YaoheWangEC/daq63050-process-signal-source/software/process-signal-source-l021k8u7-4/project/src/wk_tmr.c

/* add user code begin Header */
/**
  **************************************************************************
  * @file     wk_tmr.c
  * @brief    work bench config program
  **************************************************************************
  * Copyright (c) 2025, Artery Technology, All rights reserved.
  *
  * The software Board Support Package (BSP) that is made available to
  * download from Artery official website is the copyrighted work of Artery.
  * Artery authorizes customers to use, copy, and distribute the BSP
  * software and its related documentation for the purpose of design and
  * development in conjunction with Artery microcontrollers. Use of the
  * software is governed by this copyright notice and the following disclaimer.
  *
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
  **************************************************************************
  */
/* add user code end Header */

/* Includes ------------------------------------------------------------------*/
#include "wk_tmr.h"

/* add user code begin 0 */

/* add user code end 0 */

/**
  * @brief  init tmr3 function.
  * @param  none
  * @retval none
  */
void wk_tmr3_init(void)
{
  /* add user code begin tmr3_init 0 */

  /* add user code end tmr3_init 0 */

  gpio_init_type gpio_init_struct;
  tmr_output_config_type tmr_output_struct;

  gpio_default_para_init(&gpio_init_struct);

  /* add user code begin tmr3_init 1 */

  /* add user code end tmr3_init 1 */

  /* configure the tmr3 CH1 pin */
  gpio_pin_mux_config(GPIOA, GPIO_PINS_SOURCE6, GPIO_MUX_1);
  gpio_init_struct.gpio_pins = GPIO_PINS_6;
  gpio_init_struct.gpio_mode = GPIO_MODE_MUX;
  gpio_init_struct.gpio_out_type = GPIO_OUTPUT_PUSH_PULL;
  gpio_init_struct.gpio_pull = GPIO_PULL_NONE;
  gpio_init_struct.gpio_drive_strength = GPIO_DRIVE_STRENGTH_MODERATE;
  gpio_init(GPIOA, &gpio_init_struct);

  /* configure the tmr3 CH2 pin */
  gpio_pin_mux_config(GPIOA, GPIO_PINS_SOURCE7, GPIO_MUX_1);
  gpio_init_struct.gpio_pins = GPIO_PINS_7;
  gpio_init_struct.gpio_mode = GPIO_MODE_MUX;
  gpio_init_struct.gpio_out_type = GPIO_OUTPUT_PUSH_PULL;
  gpio_init_struct.gpio_pull = GPIO_PULL_NONE;
  gpio_init_struct.gpio_drive_strength = GPIO_DRIVE_STRENGTH_MODERATE;
  gpio_init(GPIOA, &gpio_init_struct);

  /* configure the tmr3 CH3 pin */
  gpio_pin_mux_config(GPIOB, GPIO_PINS_SOURCE0, GPIO_MUX_1);
  gpio_init_struct.gpio_pins = GPIO_PINS_0;
  gpio_init_struct.gpio_mode = GPIO_MODE_MUX;
  gpio_init_struct.gpio_out_type = GPIO_OUTPUT_PUSH_PULL;
  gpio_init_struct.gpio_pull = GPIO_PULL_NONE;
  gpio_init_struct.gpio_drive_strength = GPIO_DRIVE_STRENGTH_MODERATE;
  gpio_init(GPIOB, &gpio_init_struct);

  /* configure counter settings */
  tmr_cnt_dir_set(TMR3, TMR_COUNT_UP);
  tmr_clock_source_div_set(TMR3, TMR_CLOCK_DIV1);
  tmr_period_buffer_enable(TMR3, FALSE);
  tmr_base_init(TMR3, 999, 0);

  /* configure primary mode settings */
  tmr_sub_sync_mode_set(TMR3, FALSE);
  tmr_primary_mode_select(TMR3, TMR_PRIMARY_SEL_RESET);

  /* configure channel 1 output settings */
  tmr_output_struct.oc_mode = TMR_OUTPUT_CONTROL_PWM_MODE_A;
  tmr_output_struct.oc_output_state = TRUE;
  tmr_output_struct.occ_output_state = FALSE;
  tmr_output_struct.oc_polarity = TMR_OUTPUT_ACTIVE_HIGH;
  tmr_output_struct.occ_polarity = TMR_OUTPUT_ACTIVE_HIGH;
  tmr_output_struct.oc_idle_state = FALSE;
  tmr_output_struct.occ_idle_state = FALSE;
  tmr_output_channel_config(TMR3, TMR_SELECT_CHANNEL_1, &tmr_output_struct);
  tmr_channel_value_set(TMR3, TMR_SELECT_CHANNEL_1, 0);
  tmr_output_channel_buffer_enable(TMR3, TMR_SELECT_CHANNEL_1, FALSE);

  tmr_output_channel_immediately_set(TMR3, TMR_SELECT_CHANNEL_1, FALSE);

  /* configure channel 2 output settings */
  tmr_output_struct.oc_mode = TMR_OUTPUT_CONTROL_PWM_MODE_A;
  tmr_output_struct.oc_output_state = TRUE;
  tmr_output_struct.occ_output_state = FALSE;
  tmr_output_struct.oc_polarity = TMR_OUTPUT_ACTIVE_HIGH;
  tmr_output_struct.occ_polarity = TMR_OUTPUT_ACTIVE_HIGH;
  tmr_output_struct.oc_idle_state = FALSE;
  tmr_output_struct.occ_idle_state = FALSE;
  tmr_output_channel_config(TMR3, TMR_SELECT_CHANNEL_2, &tmr_output_struct);
  tmr_channel_value_set(TMR3, TMR_SELECT_CHANNEL_2, 0);
  tmr_output_channel_buffer_enable(TMR3, TMR_SELECT_CHANNEL_2, FALSE);

  tmr_output_channel_immediately_set(TMR3, TMR_SELECT_CHANNEL_2, FALSE);

  /* configure channel 3 output settings */
  tmr_output_struct.oc_mode = TMR_OUTPUT_CONTROL_PWM_MODE_A;
  tmr_output_struct.oc_output_state = TRUE;
  tmr_output_struct.occ_output_state = FALSE;
  tmr_output_struct.oc_polarity = TMR_OUTPUT_ACTIVE_HIGH;
  tmr_output_struct.occ_polarity = TMR_OUTPUT_ACTIVE_HIGH;
  tmr_output_struct.oc_idle_state = FALSE;
  tmr_output_struct.occ_idle_state = FALSE;
  tmr_output_channel_config(TMR3, TMR_SELECT_CHANNEL_3, &tmr_output_struct);
  tmr_channel_value_set(TMR3, TMR_SELECT_CHANNEL_3, 0);
  tmr_output_channel_buffer_enable(TMR3, TMR_SELECT_CHANNEL_3, FALSE);

  tmr_output_channel_immediately_set(TMR3, TMR_SELECT_CHANNEL_3, FALSE);


  tmr_counter_enable(TMR3, TRUE);

  /* add user code begin tmr3_init 2 */

  /* add user code end tmr3_init 2 */
}

/**
  * @brief  init tmr6 function.
  * @param  none
  * @retval none
  */
void wk_tmr6_init(void)
{
  /* add user code begin tmr6_init 0 */

  /* add user code end tmr6_init 0 */

  /* add user code begin tmr6_init 1 */

  /* add user code end tmr6_init 1 */

  /* configure counter settings */
  tmr_cnt_dir_set(TMR6, TMR_COUNT_UP);
  tmr_period_buffer_enable(TMR6, FALSE);
  tmr_base_init(TMR6, 999, 63);

  /* configure primary mode settings */
  tmr_primary_mode_select(TMR6, TMR_PRIMARY_SEL_RESET);

  tmr_counter_enable(TMR6, TRUE);

  /* enable ovfien interrupt */
  tmr_interrupt_enable(TMR6, TMR_OVF_INT, TRUE);

  /* add user code begin tmr6_init 2 */

  /* add user code end tmr6_init 2 */
}

/**
  * @brief  init tmr14 function.
  * @param  none
  * @retval none
  */
void wk_tmr14_init(void)
{
  /* add user code begin tmr14_init 0 */

  /* add user code end tmr14_init 0 */


  /* add user code begin tmr14_init 1 */

  /* add user code end tmr14_init 1 */

  /* configure counter settings */
  tmr_cnt_dir_set(TMR14, TMR_COUNT_UP);
  tmr_clock_source_div_set(TMR14, TMR_CLOCK_DIV1);
  tmr_period_buffer_enable(TMR14, FALSE);
  tmr_base_init(TMR14, 19, 63);

  tmr_counter_enable(TMR14, TRUE);

  /* enable ovfien interrupt */
  tmr_interrupt_enable(TMR14, TMR_OVF_INT, TRUE);

  /* add user code begin tmr14_init 2 */

  /* add user code end tmr14_init 2 */
}

/**
  * @brief  init tmr15 function.
  * @param  none
  * @retval none
  */
void wk_tmr15_init(void)
{
  /* add user code begin tmr15_init 0 */

  /* add user code end tmr15_init 0 */

  tmr_output_config_type tmr_output_struct;
  tmr_brkdt_config_type tmr_brkdt_struct;

  /* add user code begin tmr15_init 1 */

  /* add user code end tmr15_init 1 */

  /* configure counter settings */
  tmr_cnt_dir_set(TMR15, TMR_COUNT_UP);
  tmr_clock_source_div_set(TMR15, TMR_CLOCK_DIV1);
  tmr_repetition_counter_set(TMR15, 0);
  tmr_period_buffer_enable(TMR15, FALSE);
  tmr_base_init(TMR15, 999, 63);

  /* configure primary mode settings */
  tmr_sub_sync_mode_set(TMR15, FALSE);
  tmr_primary_mode_select(TMR15, TMR_PRIMARY_SEL_RESET);

  /* configure overflow event */
  tmr_overflow_request_source_set(TMR15, TRUE);

  /* configure channel 1 output settings */
  tmr_output_struct.oc_mode = TMR_OUTPUT_CONTROL_PWM_MODE_A;
  tmr_output_struct.oc_output_state = TRUE;
  tmr_output_struct.occ_output_state = FALSE;
  tmr_output_struct.oc_polarity = TMR_OUTPUT_ACTIVE_HIGH;
  tmr_output_struct.occ_polarity = TMR_OUTPUT_ACTIVE_HIGH;
  tmr_output_struct.oc_idle_state = FALSE;
  tmr_output_struct.occ_idle_state = FALSE;
  tmr_output_channel_config(TMR15, TMR_SELECT_CHANNEL_1, &tmr_output_struct);
  tmr_channel_value_set(TMR15, TMR_SELECT_CHANNEL_1, 499);
  tmr_output_channel_buffer_enable(TMR15, TMR_SELECT_CHANNEL_1, FALSE);

  tmr_output_channel_immediately_set(TMR15, TMR_SELECT_CHANNEL_1, FALSE);

  /* configure break and dead-time settings */
  tmr_brkdt_struct.brk_enable = FALSE;
  tmr_brkdt_struct.auto_output_enable = FALSE;
  tmr_brkdt_struct.brk_polarity = TMR_BRK_INPUT_ACTIVE_LOW;
  tmr_brkdt_struct.fcsoen_state = FALSE;
  tmr_brkdt_struct.fcsodis_state = FALSE;
  tmr_brkdt_struct.wp_level = TMR_WP_OFF;
  tmr_brkdt_struct.deadtime = 0;
  tmr_brkdt_config(TMR15, &tmr_brkdt_struct);
  
  tmr_brk_filter_value_set(TMR15, 0);

  tmr_output_enable(TMR15, TRUE);

  tmr_counter_enable(TMR15, TRUE);

  /* add user code begin tmr15_init 2 */

  /* add user code end tmr15_init 2 */
}

/* add user code begin 1 */

/* add user code end 1 */
