YaoheWangEC/daq63050-process-signal-source/software/process-signal-source-l021k8u7-4/project/src/wk_usart.c

/* add user code begin Header */
/**
  **************************************************************************
  * @file     wk_usart.c
  * @brief    work bench config program
  **************************************************************************
  * Copyright (c) 2025, Artery Technology, All rights reserved.
  *
  * The software Board Support Package (BSP) that is made available to
  * download from Artery official website is the copyrighted work of Artery.
  * Artery authorizes customers to use, copy, and distribute the BSP
  * software and its related documentation for the purpose of design and
  * development in conjunction with Artery microcontrollers. Use of the
  * software is governed by this copyright notice and the following disclaimer.
  *
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
  **************************************************************************
  */
/* add user code end Header */

/* Includes ------------------------------------------------------------------*/
#include "wk_usart.h"

/* add user code begin 0 */

/* add user code end 0 */

/**
  * @brief  init usart1 function
  * @param  none
  * @retval none
  */
void wk_usart1_init(void)
{
  /* add user code begin usart1_init 0 */

  /* add user code end usart1_init 0 */

  gpio_init_type gpio_init_struct;
  gpio_default_para_init(&gpio_init_struct);

  /* add user code begin usart1_init 1 */

  /* add user code end usart1_init 1 */

  /* configure the TX pin */
  gpio_pin_mux_config(GPIOA, GPIO_PINS_SOURCE9, GPIO_MUX_1);
  gpio_init_struct.gpio_drive_strength = GPIO_DRIVE_STRENGTH_MODERATE;
  gpio_init_struct.gpio_out_type = GPIO_OUTPUT_PUSH_PULL;
  gpio_init_struct.gpio_mode = GPIO_MODE_MUX;
  gpio_init_struct.gpio_pins = GPIO_PINS_9;
  gpio_init_struct.gpio_pull = GPIO_PULL_NONE;
  gpio_init(GPIOA, &gpio_init_struct);

  /* config usart1 clock source */
  crm_usart_clock_select(CRM_USART1, CRM_USART_CLOCK_SOURCE_PCLK);

  /* configure param */
  usart_init(USART1, 115200, USART_DATA_8BITS, USART_STOP_1_BIT);
  usart_transmitter_enable(USART1, TRUE);
  usart_parity_selection_config(USART1, USART_PARITY_NONE);

  usart_hardware_flow_control_set(USART1, USART_HARDWARE_FLOW_NONE);

  /* add user code begin usart1_init 2 */

  /* add user code end usart1_init 2 */

  usart_enable(USART1, TRUE);

  /* add user code begin usart1_init 3 */

  /* add user code end usart1_init 3 */
}

/**
  * @brief  init usart4 function
  * @param  none
  * @retval none
  */
void wk_usart4_init(void)
{
  /* add user code begin usart4_init 0 */

  /* add user code end usart4_init 0 */

  gpio_init_type gpio_init_struct;
  gpio_default_para_init(&gpio_init_struct);

  /* add user code begin usart4_init 1 */

  /* add user code end usart4_init 1 */

  /* configure the TX pin */
  gpio_pin_mux_config(GPIOA, GPIO_PINS_SOURCE0, GPIO_MUX_4);
  gpio_init_struct.gpio_drive_strength = GPIO_DRIVE_STRENGTH_MODERATE;
  gpio_init_struct.gpio_out_type = GPIO_OUTPUT_PUSH_PULL;
  gpio_init_struct.gpio_mode = GPIO_MODE_MUX;
  gpio_init_struct.gpio_pins = GPIO_PINS_0;
  gpio_init_struct.gpio_pull = GPIO_PULL_NONE;
  gpio_init(GPIOA, &gpio_init_struct);

  /* configure the RX pin */
  gpio_pin_mux_config(GPIOA, GPIO_PINS_SOURCE1, GPIO_MUX_4);
  gpio_init_struct.gpio_drive_strength = GPIO_DRIVE_STRENGTH_MODERATE;
  gpio_init_struct.gpio_out_type = GPIO_OUTPUT_PUSH_PULL;
  gpio_init_struct.gpio_mode = GPIO_MODE_MUX;
  gpio_init_struct.gpio_pins = GPIO_PINS_1;
  gpio_init_struct.gpio_pull = GPIO_PULL_NONE;
  gpio_init(GPIOA, &gpio_init_struct);

  /* configure param */
  usart_init(USART4, 115200, USART_DATA_8BITS, USART_STOP_1_BIT);
  usart_transmitter_enable(USART4, TRUE);
  usart_receiver_enable(USART4, TRUE);
  usart_parity_selection_config(USART4, USART_PARITY_NONE);

  usart_dma_transmitter_enable(USART4, TRUE);

  usart_dma_receiver_enable(USART4, TRUE);

  usart_hardware_flow_control_set(USART4, USART_HARDWARE_FLOW_NONE);

  /* enable idle interrupt */
  usart_interrupt_enable(USART4, USART_IDLE_INT, TRUE);

  /* add user code begin usart4_init 2 */

  /* add user code end usart4_init 2 */

  usart_enable(USART4, TRUE);
  
  /* add user code begin usart4_init 3 */

  /* add user code end usart4_init 3 */
}

/* add user code begin 1 */

/* add user code end 1 */
