YaoheWangEC/daq63050-process-signal-source/software/process-signal-source-l021k8u7-4/project/MDK_V5/process-signal-source/command/command_handler.h

#ifndef COMMAND_HANDLER_H
#define COMMAND_HANDLER_H

#include <stdint.h>

char* lscmd_handler(int argc, char **argv);
char* echo_handler(int argc, char **argv);
char* device_handler(int argc, char **argv);
char* mode_handler(int argc, char **argv);
char* offset_handler(int argc, char **argv);
char* vpp_handler(int argc, char **argv);
char* status_handler(int argc, char **argv);

#endif // COMMAND_HANDLER_H
